vincentbanguyen/ECE395-Poker-Card-Classifier-Device/Playing Card Classifier Model/dataset/usertest/DA-5.jpg

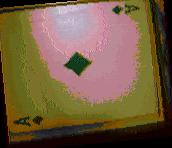
Playing Card Classifier Model/dataset/usertest/DA-5.jpg
