vincentbanguyen/ECE395-Poker-Card-Classifier-Device/Playing Card Classifier Model/dataset/usertest/DA-2.jpg

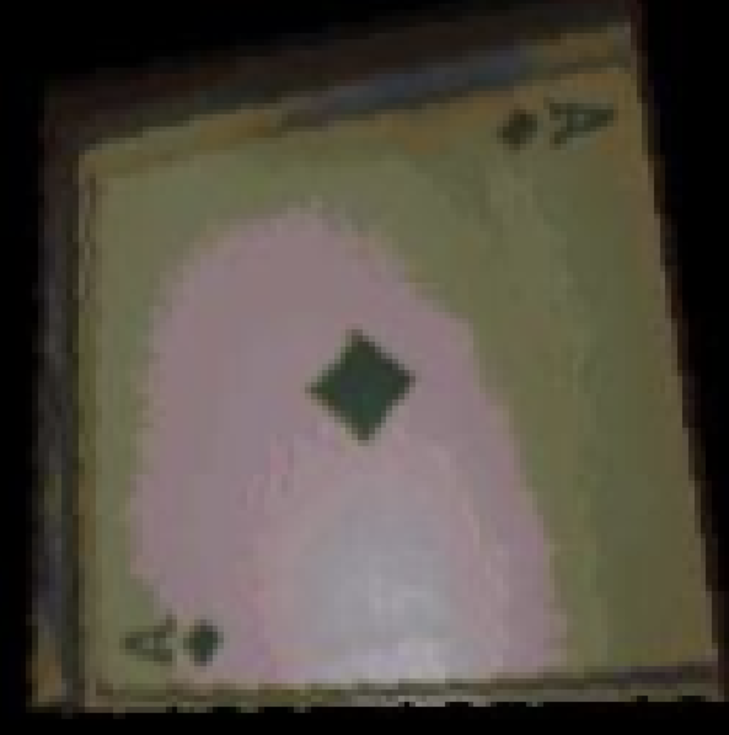
Playing Card Classifier Model/dataset/usertest/DA-2.jpg
