vincentbanguyen/ECE395-Poker-Card-Classifier-Device/Playing Card Classifier Model/dataset/usertest/2spade.jpg

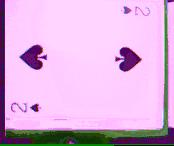
Playing Card Classifier Model/dataset/usertest/2spade.jpg
