vincentbanguyen/ECE395-Poker-Card-Classifier-Device/Playing Card Classifier Model/dataset/usertest/DA.jpg

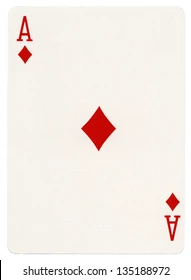
Playing Card Classifier Model/dataset/usertest/DA.jpg
