vincentbanguyen/ECE395-Poker-Card-Classifier-Device/CardClassifier/CardClassifier/X-CUBE-AI/App/network2_config.h

/**
  ******************************************************************************
  * @file    network2_config.h
  * @author  AST Embedded Analytics Research Platform
  * @date    Tue Apr 16 15:53:52 2024
  * @brief   AI Tool Automatic Code Generator for Custom Layers Implementation
  ******************************************************************************
  * @attention
  *
  * Copyright (c) 2024 STMicroelectronics.
  * All rights reserved.
  *
  * This software is licensed under terms that can be found in the LICENSE file
  * in the root directory of this software component.
  * If no LICENSE file comes with this software, it is provided AS-IS.
  ******************************************************************************
  */

#ifndef AI_NETWORK2_CONFIG_H
#define AI_NETWORK2_CONFIG_H
#pragma once

#undef AI_TOOLS_VERSION_MAJOR
#undef AI_TOOLS_VERSION_MINOR
#undef AI_TOOLS_VERSION_MICRO
#define AI_TOOLS_VERSION_MAJOR 8
#define AI_TOOLS_VERSION_MINOR 1
#define AI_TOOLS_VERSION_MICRO 0
#define AI_TOOLS_VERSION_EXTRA "19520"


#undef AI_PLATFORM_API_MAJOR
#undef AI_PLATFORM_API_MINOR
#undef AI_PLATFORM_API_MICRO
#define AI_PLATFORM_API_MAJOR       (1)
#define AI_PLATFORM_API_MINOR       (1)
#define AI_PLATFORM_API_MICRO       (0)

#undef AI_TOOLS_API_VERSION_MAJOR
#undef AI_TOOLS_API_VERSION_MINOR
#undef AI_TOOLS_API_VERSION_MICRO
#define AI_TOOLS_API_VERSION_MAJOR (1)
#define AI_TOOLS_API_VERSION_MINOR (5)
#define AI_TOOLS_API_VERSION_MICRO (0)

#endif /*AI_NETWORK2_CONFIG_H*/
